M256XR/PortaRe0/Claude/CLOSING.md

# PortaRe0 セッション終了処理

「終了処理して」と言われたら以下を自動で実行すること。

---

## 手順

1. **セッション原文を保存**
   ```
   python Claude/extract_session.py
   ```
   → `chat_logs/原文/YYYY-MM-DD_SessionNN.txt` に保存される

2. **PROGRESS.md 更新**（原文保存後に実施）
   - 「現在の作業箇所」を今日の作業内容に合わせて更新
   - 「直近の決定事項ログ」に今日の日付とセッション番号で決定事項を追記

3. **index.md 更新**（原文ファイルのL行番号を参照しながら）
   - `chat_logs/原文/index.md` のセッション別索引に今回のセッションを追記
   - 主要トピックのL行番号はおおよその目安でOK
   - トピック別索引に新規トピックがあれば追記

4. **ドキュメント更新確認**
   - 以下のファイルに今回の変更を反映すべきか確認する：
     - `README.md`（主要コンポーネント・フェーズ状況・C番号一覧）
     - `bom/cyberdeck_bom.csv` / `bom/cyberdeck_bom.xlsx`（部品追加・変更があった場合）
     - `CLAUDE.md` / `specs/*`（仕様変更・確定事項があった場合）
   - 更新が必要なら該当箇所を修正する

5. **session_close.py 実行**（上記がすべて完了してから）
   ```
   python Claude/session_close.py "Docs: sessionNN終了処理・PROGRESS/index更新"
   ```
   → PROGRESS.md の古いログを archive/ に移動（直近4件残す）
   → git add -A + commit + push
